Slamy/Yaumataca/src/processors/mouse_c1351.hpp

/**
 * @file mouse_c1351.hpp
 * @author André Zeps
 * @brief
 * @version 0.1
 * @date 2023-08-16
 *
 * @copyright Copyright (c) 2023
 *
 */

#pragma once

#include "processors/interfaces.hpp"
#include "utility.h"

#include "c1351.pio.h"
#include "hardware/pio.h"
#include "pico/stdlib.h"

/**
 * @brief Calibration data for a single controller port
 * Provides modification for the linear interpolation as performed by
 * \ref C1351Converter::push_calibrated_value
 */
struct C1351CalibrationData {
    /// @brief clock ticks to add to achieve the most stable timing for a value
    /// of 64 on POTY
    int32_t pot_y_64_ = -1452;
    /// @brief clock ticks to add to achieve the most stable timing for a value
    /// of 191 on POTY
    int32_t pot_y_191_ = -1221;

    /// @brief clock ticks to add to achieve the most stable timing for a value
    /// of 64 on POTX
    int32_t pot_x_64_ = -1675;
    /// @brief clock ticks to add to achieve the most stable timing for a value
    /// of 191 on POTX
    int32_t pot_x_191_ = -1417;
};

/**
 * @brief Emulation of the Commodore 1351 in proportional mode.
 * Uses the POTX and POTY pins to simulate analog values for the ADC inside
 * the SID.
 *
 * http://sensi.org/~svo/%5Bm%5Douse/ was a great help here
 *
 * The measurement cycle of the SID takes 512 microseconds.
 * The first 256 are spent inside the SID by draining a capacitor.
 * The second 256 are used to wait until the capacitor is charged to a certain
 * level by an external resistor. This means that the ADC is not measuring
 * voltage but resistance and it does this nearly linear which is good for
 * paddles.
 *
 * Our goal here is wait for a defined time and charge the capacitor in a timed
 * manner to simulate a certain value in the SID that we want.
 *
 * We does this by using the PIO units of the RP2040. One PIO has 4 state
 * machines. We will use all of them to drive 2x POTX and 2x POTY
 *
 */
class C1351Converter : public RunnableMouseReportProcessor {
  private:
    /// @brief Single PIO unit for all 4 required pins.
    static PIO pio_;

    /// @brief state machine to drive POTX
    int sm_x_{-1};
    /// @brief state machine to drive POTY
    int sm_y_{-1};

    /// @brief Position of program in PIO instruction memory
    static uint offset_;

    /// @brief horizontal movement still to perform using PIO
    int32_t mouse_accumulator_x{0};
    /// @brief vertical movement still to perform using PIO
    int32_t mouse_accumulator_y{0};
    /// @brief Wheel movement still to perform using pulses
    int32_t mouse_accumulator_wheel{0};

    /// @brief Absolute time in milliseconds when the wheel signal was changed last
    /// According to the protocol, it must be held for 50ms
    uint32_t mouse_wheel_pulse_last_update{0};
    /// @brief Current wheel output pulse state
    /// If true, the port is drained right now
    bool mouse_wheel_pulse_state{false};

    /// @brief current POTX value we want to achieve
    uint32_t value_pot_x_{30};
    /// @brief current POTY value we want to achieve
    uint32_t value_pot_y_{30};

    /// @brief current mouse button state
    ControllerPortState state_;
    /// @brief last mouse button state. used to check for changes
    ControllerPortState last_state_;

    /// @brief Number of milliseconds the Wheel direction has to be kept stable
    /// According to https://wiki.icomp.de/wiki/Micromys_Protocol
    static constexpr uint32_t kWheelPulseLength{50};

    /// @brief number of microseconds the SID will drain the capacitor
    static constexpr int32_t kDrainLength = 256;
    /// @brief number of PIO clock ticks per microsecond
    static constexpr int32_t kDigitPerUs = 125;

    /// Possible modes this module can operate in
    enum class OperatingState {
        kEffective,        ///< Just doing the job it is supposed to do
        kCalibratePotX64,  ///< Calibrate lower end of usable Pot X range
        kCalibratePotX191, ///< Calibrate upper end of usable Pot X range
        kCalibratePotY64,  ///< Calibrate lower end of usable Pot Y range
        kCalibratePotY191, ///< Calibrate upper end of usable Pot Y range
    };

    /// Timing correction values for stable POT input on the SID
    /// Required because of component tolerances
    static std::array<struct C1351CalibrationData, 2> calibration_;

    /// Current active mode
    OperatingState operating_state_{OperatingState::kEffective};

    /// Time out counter to abort detection of secret button combo
    uint16_t calibration_mode_enter_timeout_{0};
    /// Number of correct button presses that are detected until
    /// now, which would lead to the calibration mode
    uint8_t calibration_mode_enter_counter_{0};

    /**
     * @brief Checks if the PIO state machines can take another value.
     *
     * Usually the FIFOs are allowed to take up to 4 values but we don't really
     * want any latency here. Only push a value if the FIFOs are both empty.
     *
     * @return true Values can be pushed
     * @return false Wait another round
     */
    bool pio_fifos_can_take_values() {
        return pio_sm_is_tx_fifo_empty(pio_, sm_y_) && pio_sm_is_tx_fifo_empty(pio_, sm_x_);
    }

    /**
     * @brief Provide PIO with drain durations to simulate a resistor
     *
     * Allowed values for C1351 are 64 to 191 according to VICE emulator.
     * This would mean that a range of 128 is available which seems to be not
     * the truth. According to https://www.c64-wiki.de/wiki/Mouse_1351, the
     * highest bit must be ignored and the lowest is considered to be a noise
     * value to help with oscillating values. This leaves us with a real range
     * of 64 values.
     *
     * @param sm            State machine to affect
     * @param pot_value     Value in range of 64 to inclusive 191
     */
    void push_calibrated_value(int sm, uint32_t pot_value) {
        float x0, y0, x1, y1, xp, yp;

        struct C1351CalibrationData &calib = calibration_.at(target_->get_index());

        if (sm == sm_y_) {
            y0 = static_cast<float>(calib.pot_y_64_);
            y1 = static_cast<float>(calib.pot_y_191_);
        } else {
            y0 = static_cast<float>(calib.pot_x_64_);
            y1 = static_cast<float>(calib.pot_x_191_);
        }

        xp = static_cast<float>(pot_value);
        x0 = 64;
        x1 = 191;
        yp = y0 + ((y1 - y0) / (x1 - x0)) * (xp - x0);

        int32_t calibration = static_cast<int32_t>(yp);

        // Make the calibration fluctuate during calibration mode
        // to improve the results after calibration.
        if (operating_state_ != OperatingState::kEffective) {
            calibration += (values_pushed_cnt_ & 0x08) ? 20 : -20;
        }

        pio_sm_put(pio_, sm, (kDrainLength + pot_value) * kDigitPerUs + calibration);
    }

    /// @brief  data sink for mouse button presses
    /// Also used to gather POTX and POTY pin numbers to configure the PIO
    /// machine
    std::shared_ptr<ControllerPortInterface> target_;

    /**
     * @brief Implements fractional movement speed.
     * Incremented every time a new value is pushed to the PIO which is done
     * every 512us.
     * But the C64 is unable to process much movement as it seems, so we use
     * this value to allow faster movement for some time to have fractional
     * speeds without floating point calculations. Look at the code of \ref run
     * for an example.
     *
     */
    uint32_t values_pushed_cnt_{0};

    /// @brief Stores calibration data to Flash
    static void save_calibration_data();

  public:
    /// @brief Loads calibration data from Flash
    static void load_calibration_data();

    C1351Converter() {
        PRINTF("C1351Converter +\n");
    }
    virtual ~C1351Converter() {
        PRINTF("C1351Converter -\n");
    }

    /**
     * @brief Registers a data sink for mouse button clicks.
     *
     * Keep in mind that the movement is not done using GPIO but PIO
     * and all that is not handled in the implementations of \ref
     * ControllerPortInterface
     *
     * @param t     implementation of a controller port
     */
    void set_target(std::shared_ptr<ControllerPortInterface> t) {
        target_ = t;
    }

    void ensure_mouse_muxing() override {
        if (target_->get_pot_y_sense_gpio() == 8) {
            sm_x_ = 0;
            sm_y_ = 1;
        } else {
            sm_x_ = 2;
            sm_y_ = 3;
        }
        pio_sm_set_enabled(pio_, sm_x_, false);
        pio_sm_set_enabled(pio_, sm_y_, false);

        sid_adc_stim_program_init(pio_, sm_x_, offset_, target_->get_pot_y_sense_gpio(),
                                  target_->get_pot_x_drain_gpio());
        sid_adc_stim_program_init(pio_, sm_y_, offset_, target_->get_pot_y_sense_gpio(),
                                  target_->get_pot_y_drain_gpio());

        PRINTF("Enable C1351 for %s port\n", target_->get_name());
    }

    /**
     * @brief Initialize PIO hardware.
     *
     * Must be called once before using the PIO.
     */
    static void setup_pio() {
        pio_ = reinterpret_cast<PIO>(PIO0_BASE);
        offset_ = pio_add_program(pio_, &sid_adc_stim_program);
    }

    /**
     * @brief Detects button combination for entering calibration mode
     *
     * Detects the button combination of mouse buttons LLRRRL
     * without much mouse cursor movement in between.
     *
     * @return true
     * @return false
     */
    bool check_calibration_mode_enter_criteria() {

        // How many times was this function called
        // without progressing the state machine?
        // Decrease calibration_mode_enter_timeout_ each
        // time and abort the detection of the button
        // combination.
        if (calibration_mode_enter_timeout_) {
            calibration_mode_enter_timeout_--;
            if (calibration_mode_enter_timeout_ == 0) {
                calibration_mode_enter_counter_ = 0;
            }
        }

        switch (calibration_mode_enter_counter_) {
        case 0:
        case 1:
            if (state_.fire1 && !last_state_.fire1) {
                PRINTF("Calib up!\n");
                calibration_mode_enter_counter_++;
                calibration_mode_enter_timeout_ = 5;
            }

            if (state_.up && !last_state_.up) {
                // PRINTF("Calib force down!\n");
                calibration_mode_enter_counter_ = 0;
            }
            break;
        case 2:
        case 3:
        case 4:
            if (state_.up && !last_state_.up) {
                calibration_mode_enter_counter_++;
                calibration_mode_enter_timeout_ = 5;
            }

            if (state_.fire1 && !last_state_.fire1) {
                PRINTF("Calib force down!\n");
                calibration_mode_enter_counter_ = 0;
            }
            break;
        case 5:
            if (state_.down && !last_state_.down) {
                calibration_mode_enter_counter_ = 0;
                // Full combination detected
                return true;
            }

            if (state_.up && !last_state_.up) {
                PRINTF("Calib force down!\n");
                calibration_mode_enter_counter_ = 0;
            }
            break;
        }

        return false;
    }

    void process_mouse_report(MouseReport &mouse_report) override {
        state_.fire1 = mouse_report.left;
        state_.up = mouse_report.right;
        state_.down = mouse_report.middle;

        struct C1351CalibrationData &calib = calibration_.at(target_->get_index());

        switch (operating_state_) {
        case OperatingState::kEffective:
            mouse_accumulator_x += mouse_report.relx;
            mouse_accumulator_y -= mouse_report.rely;
            mouse_accumulator_wheel += mouse_report.wheel;

            if (check_calibration_mode_enter_criteria()) {
                operating_state_ = OperatingState::kCalibratePotX64;
                PRINTF("To kCalibratePotX64\n");
            }
            break;
        case OperatingState::kCalibratePotX64:
            calib.pot_x_64_ += mouse_report.wheel;

            if (state_.fire1 && !last_state_.fire1) {
                operating_state_ = OperatingState::kCalibratePotX191;
                PRINTF("To kCalibratePotX191\n");
            }
            break;
        case OperatingState::kCalibratePotX191:
            calib.pot_x_191_ += mouse_report.wheel;
            if (state_.fire1 && !last_state_.fire1) {
                operating_state_ = OperatingState::kCalibratePotY64;
                PRINTF("To kCalibratePotY64\n");
            }
            break;
        case OperatingState::kCalibratePotY64:
            calib.pot_y_64_ += mouse_report.wheel;
            if (state_.fire1 && !last_state_.fire1) {
                operating_state_ = OperatingState::kCalibratePotY191;
                PRINTF("To kCalibratePotY191\n");
            }
            break;
        case OperatingState::kCalibratePotY191:
            calib.pot_y_191_ += mouse_report.wheel;
            if (state_.fire1 && !last_state_.fire1) {
                operating_state_ = OperatingState::kEffective;
                PRINTF("Calibration finished! %ld %ld %ld %ld\n", calib.pot_x_64_, calib.pot_x_191_, calib.pot_y_64_,
                       calib.pot_y_191_);
                save_calibration_data();
            }
            break;
        }

        // Right mouse button to abort
        if (operating_state_ != OperatingState::kEffective && state_.up && !last_state_.up) {
            PRINTF("Aborted calibration\n");
            operating_state_ = OperatingState::kEffective;
            load_calibration_data();
        }

        if (target_ && last_state_ != state_) {
            last_state_ = state_;
            target_->set_port_state(state_);
        }
    }

    /**
     * @brief Provides new pot values for the C1351 emulation.
     *
     * The SID has a measuring cycle of 512 microsecond for the
     * POT X and Y pins. The range of values is 64 as explained in \ref
     * C1351Converter::push_calibrated_value. This would mean that it should
     * be possible to have a diff of 30 between measurement cycles. This is
     * not the case at least with "THE FINAL CARTRIDGE III" as the reading
     * frequency of POT X and Y from the software is much lower than what
     * the SID can do.
     *
     * I tried to solve this here by limiting the amount of change for every
     * measuring cycle to 2. This would mean that the change is limited to
     * 40 per frame, assuming that a frame takes 20 milliseconds. Without
     * the noise bit this would mean the change is limited to 20 per frame.
     * This is weird because I would assume that 30 must be possible as
     * well, but 3 is too much for "DESKTOP V1.0" of "THE FINAL CARTRIDGE
     * III".
     *
     * Then let's go for a fraction here. 2 times out of 8 it is 3, else 2.
     * This limits it to 2.25 which seems to be fine with "DESKTOP V1.0"
     * But not for Lemmings. I've performed measurements and the fastest
     * speed is 1.5 so I'm going for that until I find another incompatible
     * software.
     */
    void run() override {
        static constexpr uint8_t kNotCalibratedChanValue{25};

        if (pio_fifos_can_take_values()) {
            values_pushed_cnt_++;

            switch (operating_state_) {
            case OperatingState::kEffective: {
                int32_t kMaxChange = (values_pushed_cnt_ % 8) > 3 ? 2 : 1; // 1.5 per cycle

                int32_t inc_x = std::max(-kMaxChange, std::min(mouse_accumulator_x, kMaxChange));
                int32_t inc_y = std::max(-kMaxChange, std::min(mouse_accumulator_y, kMaxChange));

                mouse_accumulator_x -= inc_x;
                mouse_accumulator_y -= inc_y;
                value_pot_x_ += inc_x;
                value_pot_y_ += inc_y;

                push_calibrated_value(sm_x_, (value_pot_x_ % 128) + 64);
                push_calibrated_value(sm_y_, (value_pot_y_ % 128) + 64);
                break;
            }
            case OperatingState::kCalibratePotX64: {
                push_calibrated_value(sm_x_, 64);
                push_calibrated_value(sm_y_, kNotCalibratedChanValue);
                break;
            }
            case OperatingState::kCalibratePotX191: {
                push_calibrated_value(sm_x_, 191);
                push_calibrated_value(sm_y_, kNotCalibratedChanValue);
                break;
            }
            case OperatingState::kCalibratePotY64: {
                push_calibrated_value(sm_x_, kNotCalibratedChanValue);
                push_calibrated_value(sm_y_, 64);
                break;
            }
            case OperatingState::kCalibratePotY191: {
                push_calibrated_value(sm_x_, kNotCalibratedChanValue);
                push_calibrated_value(sm_y_, 191);
                break;
            }
            }
        }

        // Handle Micromys Wheel
        if (mouse_wheel_pulse_state) {
            // Right now, we are draining either Left or Right
            uint32_t now = board_millis();
            uint32_t time_diff = now - mouse_wheel_pulse_last_update;

            // Release the drain after 50ms
            if (time_diff > kWheelPulseLength) {
                mouse_wheel_pulse_last_update = now;
                mouse_wheel_pulse_state = false;

                state_.left = 0;
                state_.right = 0;
            }
        } else if (mouse_accumulator_wheel != 0) {
            // There are pulses to make as the Accumulator is not 0
            uint32_t now = board_millis();
            uint32_t time_diff = now - mouse_wheel_pulse_last_update;

            if (time_diff > kWheelPulseLength) {
                mouse_wheel_pulse_last_update = now;

                mouse_wheel_pulse_state = true;
                if (mouse_accumulator_wheel > 0) {
                    state_.left = 1; // Pulse Wheel Up
                    mouse_accumulator_wheel--;
                } else {
                    state_.right = 1; // Pulse Wheel Down
                    mouse_accumulator_wheel++;
                }
            }
        }

        if (target_ && last_state_ != state_) {
            last_state_ = state_;
            target_->set_port_state(state_);
        }
    }
};
